aroidzap/mikroprocesorova-vykreslovaci-jednotka/Rendering microprocessor/touch_button.c

/*
*	Copyright (c) 2015 Tomáš Pazdiora
*	See the file "LICENSE.txt" for the full license governing this code.
*/

#include "touch_button.h"

void init_touch()
{
	TOUCH_DDR|=_BV(TOUCH_SUPPLY);
	TOUCH_DDR&=~_BV(TOUCH_INPUT);
	
	TOUCH_PORT|=_BV(TOUCH_SUPPLY)|_BV(TOUCH_INPUT);
}

void wait_for_touch()
{
	while((TOUCH_PIN&_BV(TOUCH_INPUT))!=0){}
}
